jontisch/Current_probes/arduino/src/UIPEthernet/utility/uip_timer.c

/**
 * \addtogroup timer
 * @{
 */

/**
 * \file
 * Timer library implementation.
 * \author
 * Adam Dunkels <adam@sics.se>
 */

/*
 * Copyright (c) 2004, Swedish Institute of Computer Science.
 * All rights reserved.
 *
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
 * This file is part of the uIP TCP/IP stack
 *
 * Author: Adam Dunkels <adam@sics.se>
 *
 * $Id: timer.c,v 1.2 2006/06/12 08:00:30 adam Exp $
 */

#include "uip_clock.h"
#include "uip_timer.h"

/*---------------------------------------------------------------------------*/
/**
 * Set a timer.
 *
 * This function is used to set a timer for a time sometime in the
 * future. The function timer_expired() will evaluate to true after
 * the timer has expired.
 *
 * \param t A pointer to the timer
 * \param interval The interval before the timer expires.
 *
 */
void
uip_timer_set(struct uip_timer *t, clock_time_t interval)
{
  t->interval = interval;
  t->start = clock_time();
}
/*---------------------------------------------------------------------------*/
/**
 * Reset the timer with the same interval.
 *
 * This function resets the timer with the same interval that was
 * given to the timer_set() function. The start point of the interval
 * is the exact time that the timer last expired. Therefore, this
 * function will cause the timer to be stable over time, unlike the
 * timer_rester() function.
 *
 * \param t A pointer to the timer.
 *
 * \sa timer_restart()
 */
void
uip_timer_reset(struct uip_timer *t)
{
  t->start += t->interval;
}
/*---------------------------------------------------------------------------*/
/**
 * Restart the timer from the current point in time
 *
 * This function restarts a timer with the same interval that was
 * given to the timer_set() function. The timer will start at the
 * current time.
 *
 * \note A periodic timer will drift if this function is used to reset
 * it. For preioric timers, use the timer_reset() function instead.
 *
 * \param t A pointer to the timer.
 *
 * \sa timer_reset()
 */
void
uip_timer_restart(struct uip_timer *t)
{
  t->start = clock_time();
}
/*---------------------------------------------------------------------------*/
/**
 * Check if a timer has expired.
 *
 * This function tests if a timer has expired and returns true or
 * false depending on its status.
 *
 * \param t A pointer to the timer
 *
 * \return Non-zero if the timer has expired, zero otherwise.
 *
 */
int
uip_timer_expired(struct uip_timer *t)
{
  return (clock_time_t)(clock_time() - t->start) >= (clock_time_t)t->interval;
}
/*---------------------------------------------------------------------------*/

/** @} */
