jontisch/Current_probes/arduino/src/UIPEthernet/utility/clock-arch.c

/*
 clock-arch.c - Arduino implementation of uIP clock device.
 Copyright (c) 2010 Adam Nielsen <malvineous@shikadi.net>
 All rights reserved.

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
 You should have received a copy of the GNU Lesser General Public
 License along with this library; if not, write to the Free Software
 Foundation, Inc., 51 Franklin St, Fifth Floor, Boston, MA  02110-1301  USA
 */

#include <Arduino.h>
#include "clock-arch.h"

clock_time_t
clock_time(void)
{
  return (clock_time_t) millis();
}
